iilliio/Pixel-staff/Hardware/Electronics/kicad/kicad.kicad_sch

## KiCad design Hardware/Electronics/kicad/kicad.kicad_sch (2025-04-05)

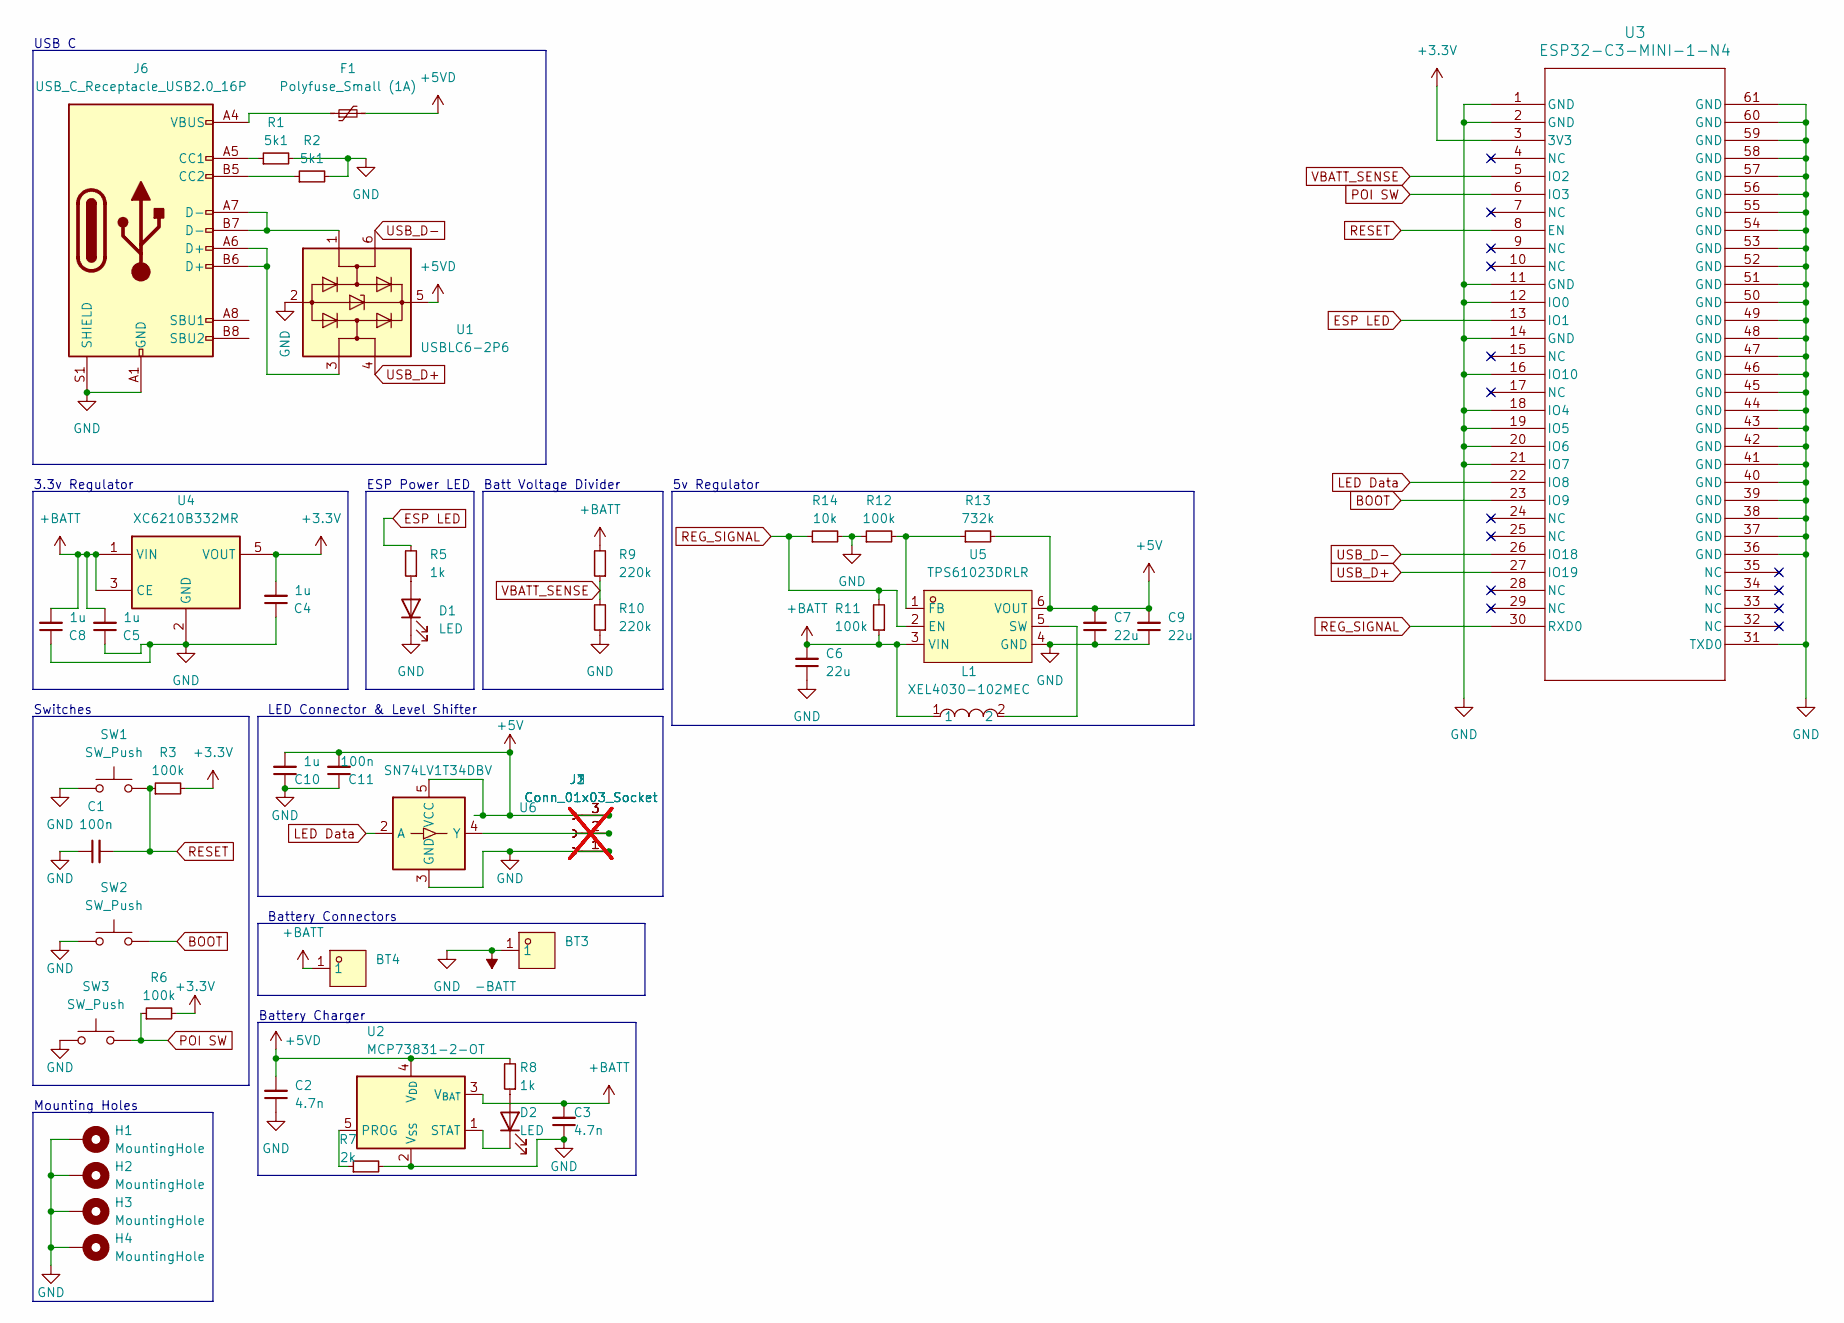
[picture p31: schematic kicad.kicad_sch]

Parts:
BT3, BT4: MY-ZJ-110; SMD_MY-ZJ-110; LCSC Part C964859
C1, C11: 100n; C_0805_2012Metric; LCSC C83055
C2, C3: 4.7n; C_0805_2012Metric; LCSC C123621
C4, C5, C8, C10: 1u; C_0805_2012Metric; LCSC C28323
C6, C7, C9: 22u; C_0805_2012Metric; LCSC C45783
D1, D2: LED; LED_0603_1608Metric; LCSC C965807
F1: Polyfuse_Small (1A); Fuse_1206_3216Metric; LCSC C720075
H1, H2, H3, H4: MountingHole; MountingHole_3.2mm_M3_Pad
J1, J2, J3: Conn_01x03_Socket; JST_PH_B3B-PH-K_1x03_P2.00mm_Vertical; not fitted
J6: USB_C_Receptacle_USB2.0_16P; USB_C_Receptacle_HRO_TYPE-C-31-M-12; LCSC C2765186
L1: XEL4030-102MEC; IND-SMD_L4.0-W4.0-A; LCSC Part C5441341
R1, R2: 5k1; R_0603_1608Metric; LCSC C14677
R3, R6, R11, R12: 100k; R_0603_1608Metric; LCSC C14675
R5, R8: 1k; R_0603_1608Metric; LCSC C22548
R7: 2k; R_0603_1608Metric; LCSC C22975
R9, R10: 220k; R_0603_1608Metric; LCSC C22961
R13: 732k; R_0603_1608Metric; LCSC C246003
R14: 10k; R_0603_1608Metric; LCSC C98220
SW1, SW2: SW_Push; SW_SPST_B3U-1000P; LCSC C231329
SW3: SW_Push; Panasonic_EVQPUL_EVQPUC; LCSC C397351
U1: USBLC6-2P6; SOT-666; LCSC C15999
U2: MCP73831-2-OT; SOT-23-5; LCSC C424093
U3: ESP32-C3-MINI-1-N4; ESP32-C3-MINI-1_EXP; LCSC C2934569
U4: XC6210B332MR; SOT-23-5; LCSC C47719
U5: TPS61023DRLR; SOT-563_L1.6-W1.2-P0.50-LS1.6-BR; LCSC Part C919459
U6: SN74LV1T34DBV; SOT-23-5; LCSC C100024

Connections:
+3.3V: C4.2, R3.2, R6.2, U3.3 (3V3), U4.5 (VOUT)
+5V: C7.2, C9.2, C10.2, C11.2, J1.3, J2.3, J3.3, R13.2, U5.6 (VOUT), U6.5 (VCC)
+5VD: C2.2, F1.2, R8.2, U1.5 (VBUS), U2.4 (V_{DD})
+BATT: BT4.1, C3.2, C5.2, C6.2, C8.2, L1.1, R9.2, R11.1, U2.3 (V_{BAT}), U4.1 (VIN), U4.3 (CE), U5.3 (VIN)
-BATT: BT3.1, C1.1, C2.1, C3.1, C4.1, C5.1, C6.1, C7.1, C8.1, C9.1, C10.1, C11.1, D1.1 (K), H1.1, H2.1, H3.1, H4.1, J1.1, J2.1, J3.1, J6.A1 (GND), J6.A12 (GND), J6.B1 (GND), J6.B12 (GND), J6.S1 (SHIELD), R1.2, R2.2, R7.2, R10.1, R12.1, R14.2, SW1.1, SW2.1, SW3.1, U1.2 (GND), U2.2 (V_{SS}), U3.1 (GND), U3.2 (GND), U3.11 (GND), U3.12 (IO0), U3.14 (GND), U3.16 (IO10), U3.18 (IO4), U3.19 (IO5), U3.20 (IO6), U3.21 (IO7), U3.31 (TXD0), U3.36 (GND), U3.37 (GND), U3.38 (GND), U3.39 (GND), U3.40 (GND), U3.41 (GND), U3.42 (GND), U3.43 (GND), U3.44 (GND), U3.45 (GND), U3.46 (GND), U3.47 (GND), U3.48 (GND), U3.49 (GND), U3.50 (GND), U3.51 (GND), U3.52 (GND), U3.53 (GND), U3.54 (GND), U3.55 (GND), U3.56 (GND), U3.57 (GND), U3.58 (GND), U3.59 (GND), U3.60 (GND), U3.61 (GND), U4.2 (GND), U5.4 (GND), U6.3 (GND)
BOOT: SW2.2, U3.23 (IO9)
ESP LED: R5.2, U3.13 (IO1)
LED Data: U3.22 (IO8), U6.2 (A)
unnamed: D1.2 (A), R5.1
unnamed: D2.1 (K), U2.1 (STAT)
unnamed: D2.2 (A), R8.1
unnamed: F1.1, J6.A4 (VBUS), J6.A9 (VBUS), J6.B4 (VBUS), J6.B9 (VBUS)
unnamed: J1.2, J2.2, J3.2, U6.4 (Y)
unnamed: J6.A5 (CC1), R1.1
unnamed: J6.A6 (D+), J6.B6 (D+), U1.3 (I/O2)
unnamed: J6.A7 (D-), J6.B7 (D-), U1.1 (I/O1)
unnamed: J6.B5 (CC2), R2.1
unnamed: L1.2, U5.5 (SW)
unnamed: R7.1, U2.5 (PROG)
unnamed: R12.2, R13.1, U5.1 (FB)
POI SW: R6.1, SW3.2, U3.6 (IO3)
REG_SIGNAL: R11.2, R14.1, U3.30 (RXD0), U5.2 (EN)
RESET: C1.2, R3.1, SW1.2, U3.8 (EN)
USB_D+: U1.4 (I/O2), U3.27 (IO19)
USB_D-: U1.6 (I/O1), U3.26 (IO18)
VBATT_SENSE: R9.1, R10.2, U3.5 (IO2)

Notes on the sheet:
Battery Connectors
Batt Voltage Divider
Mounting Holes
LED Connector & Level Shifter
USB C
5v Regulator
3.3v Regulator
ESP Power LED
Switches
Battery Charger
