iilliio/Pixel-staff/Firmware/open_pixel_poi_firmware_platformio/src/main.cpp

// Sub-Modules
#include "open_pixel_poi_led.cpp"
#include "open_pixel_poi_ble.cpp"
#include "open_pixel_poi_button.cpp"

#define DEBUG  // Comment this line out to remove printf statements in released version
#ifdef DEBUG
#define debugf(...) Serial.print("<<main>> ");Serial.printf(__VA_ARGS__);
#define debugf_noprefix(...) Serial.printf(__VA_ARGS__);
#else
#define debugf(...)
#define debugf_noprefix(...)
#endif


OpenPixelPoiConfig config;
OpenPixelPoiBLE ble(config);
OpenPixelPoiLED led(config);
OpenPixelPoiButton button(config);

void setup() {
  #ifdef DEBUG
    Serial.begin(19200);
    Serial.setDebugOutput(true);
  #endif
  //while(!Serial);  // required for Serial.print* to work correctly

  debugf("Open Pixel POI\n");
  debugf("Setup Begin\n");

  config.setup();
  led.setup();
  ble.setup();
  button.setup();
  debugf("- Setup Complete\n");
}

void loop() {
  if(!ble.flagMultipartPattern){
    ble.loop();
    config.loop();
    led.loop();
    button.loop();
  }else{
    delay(250);
    // jammed
    if(millis() - ble.bleLastReceived > 5000){
      ble.flagMultipartPattern = false;
    }
  }
}
